CircuitSetup/Split-Single-Phase-Energy-Meter/Hardware/energy_meter_pcb_v1.3_back.PNG

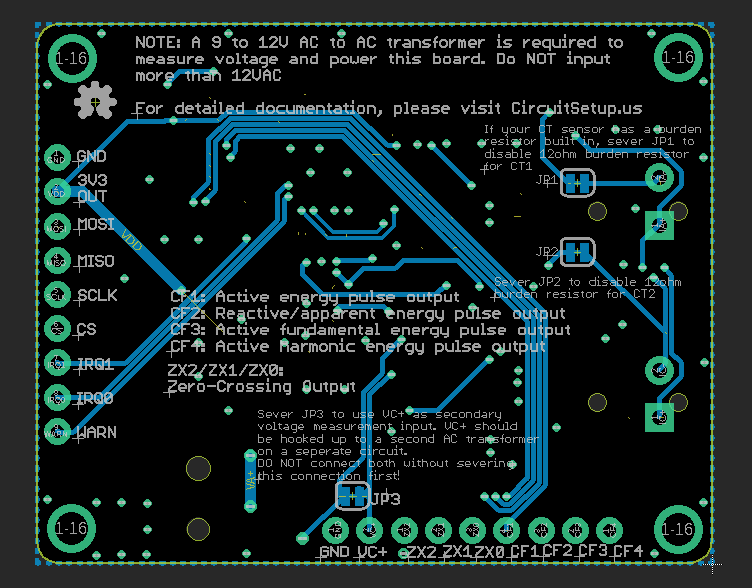
Hardware/energy_meter_pcb_v1.3_back.PNG
