CircuitSetup/Split-Single-Phase-Energy-Meter/Hardware/energy_meter_pcb_v1.4.png

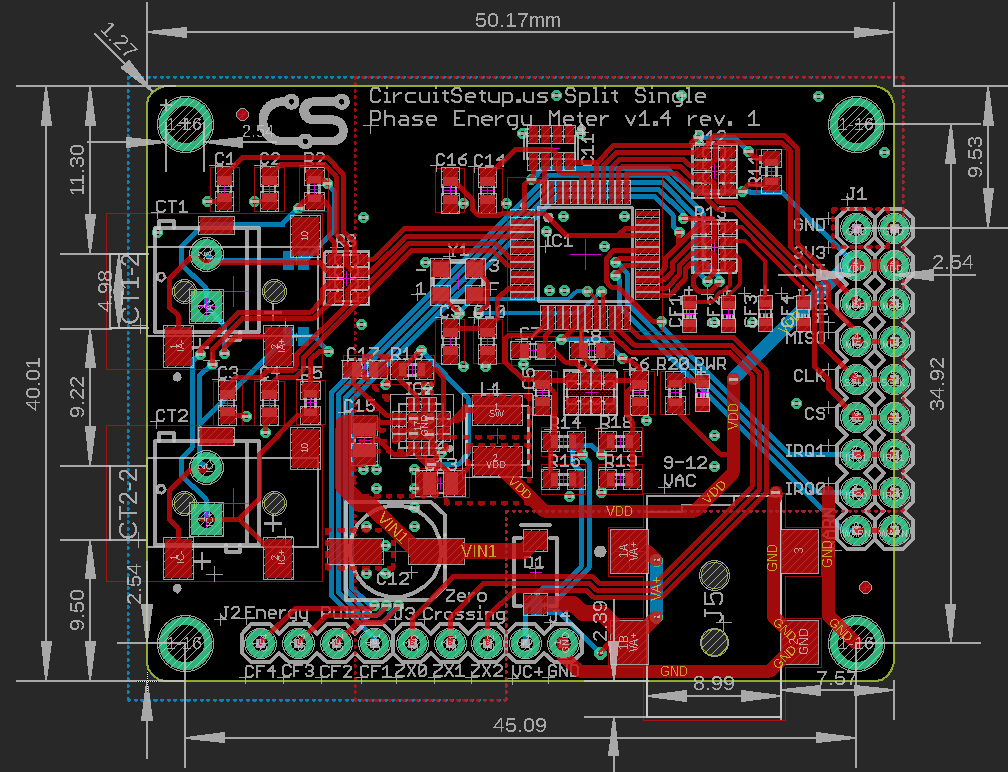
Hardware/energy_meter_pcb_v1.4.png
