CircuitSetup/Split-Single-Phase-Energy-Meter/Hardware/energy_meter_schematic.png

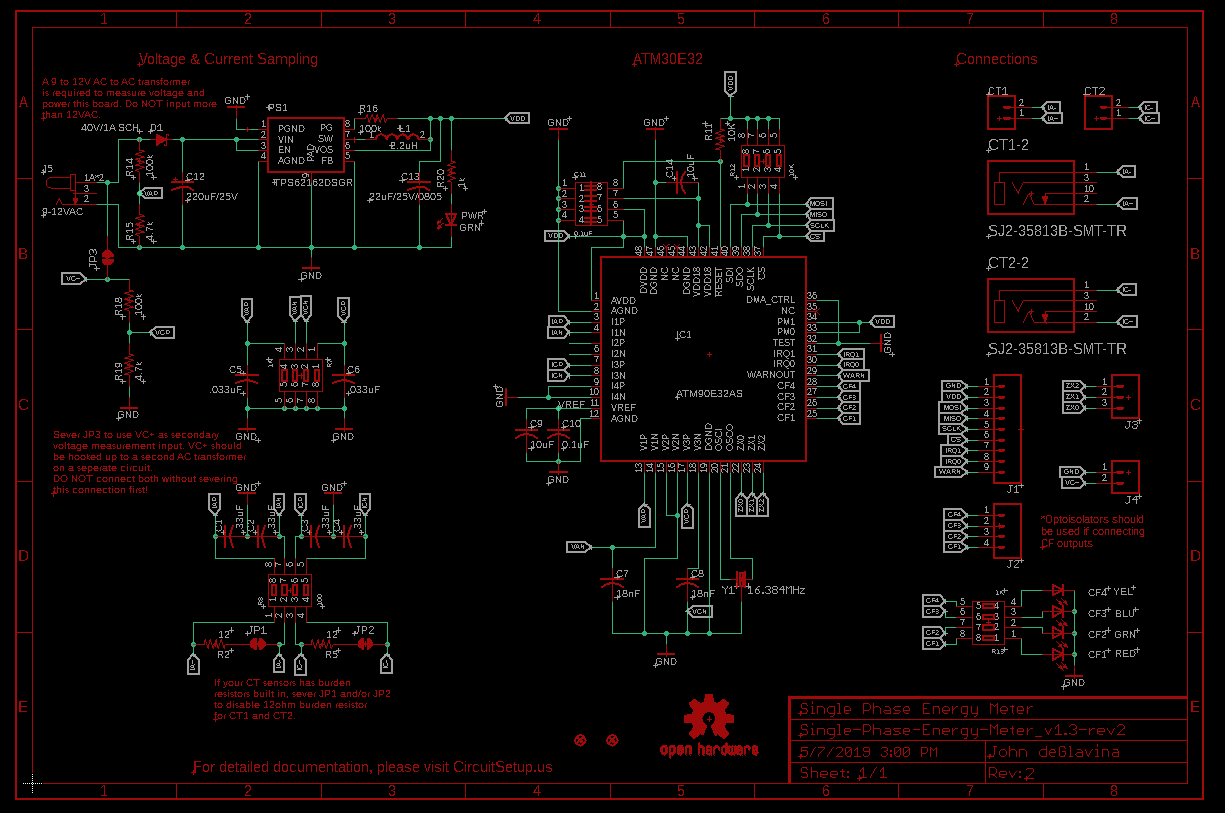
Hardware/energy_meter_schematic.png
