CircuitSetup/Split-Single-Phase-Energy-Meter/Hardware/energy_meter_schematic_v1.4.png

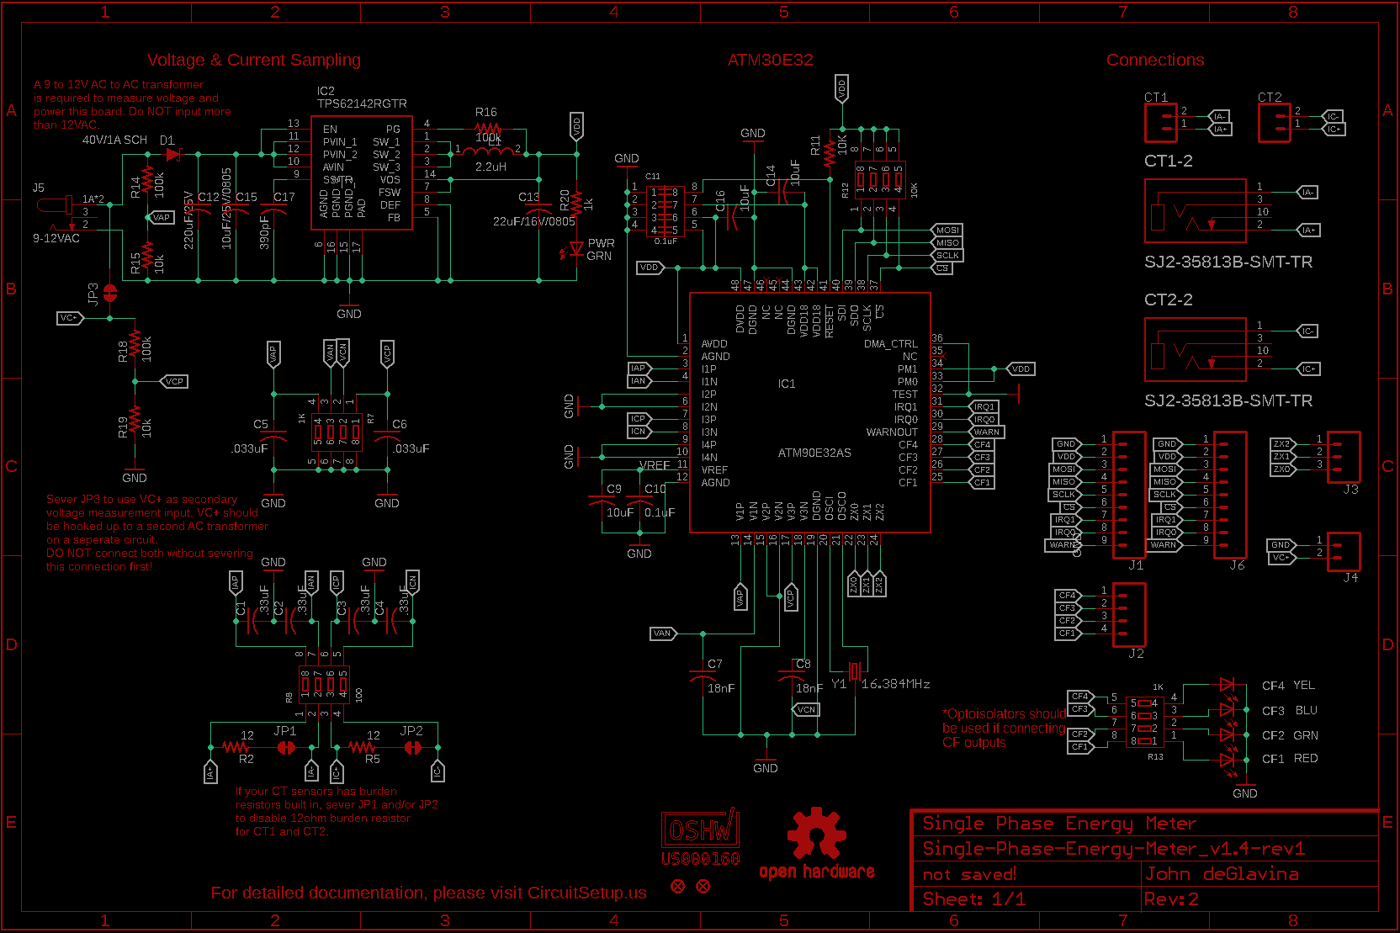
Hardware/energy_meter_schematic_v1.4.png
