CircuitSetup/Split-Single-Phase-Energy-Meter/Hardware/solar_adapter_esp32-oled.PNG

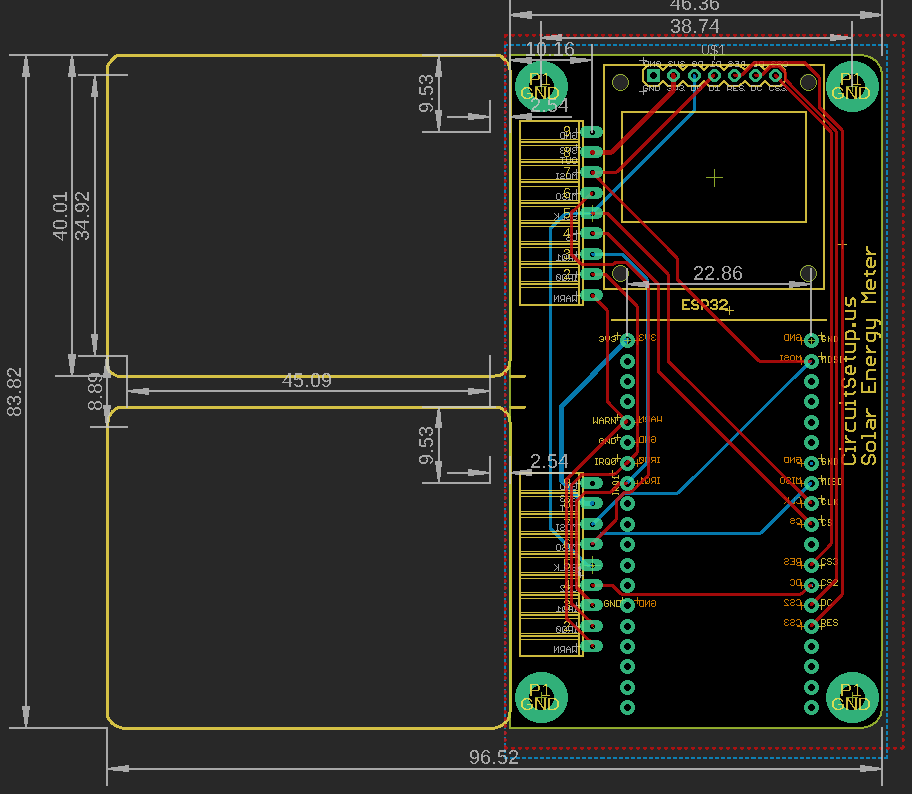
Hardware/solar_adapter_esp32-oled.PNG
