CircuitSetup/Split-Single-Phase-Energy-Meter/images/2EwjojQ.png

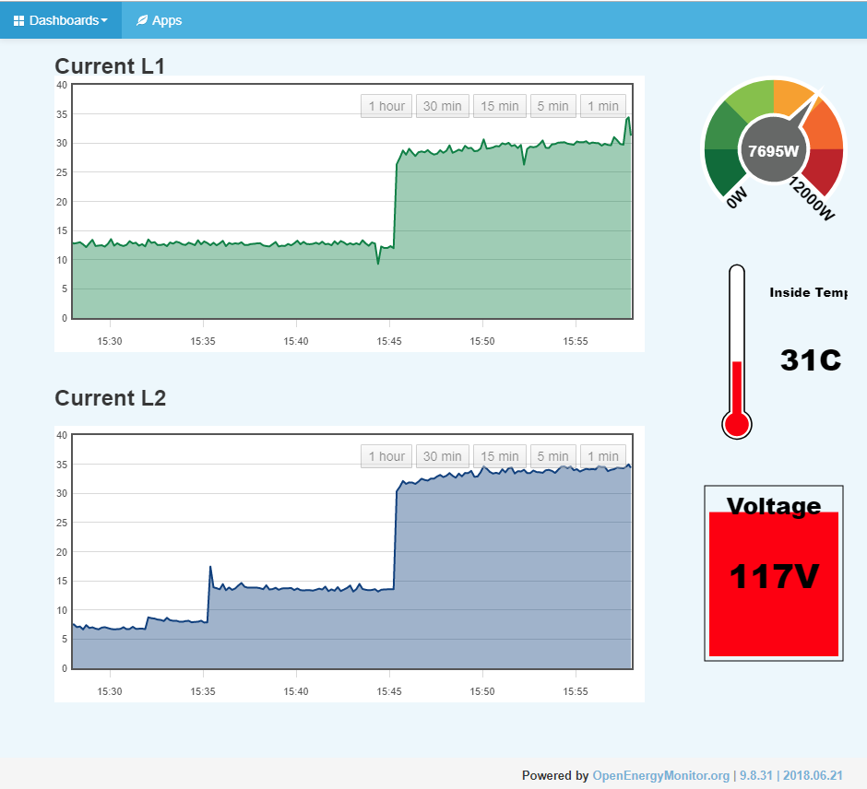
images/2EwjojQ.png
