CircuitSetup/Split-Single-Phase-Energy-Meter/images/9XtFifv.png

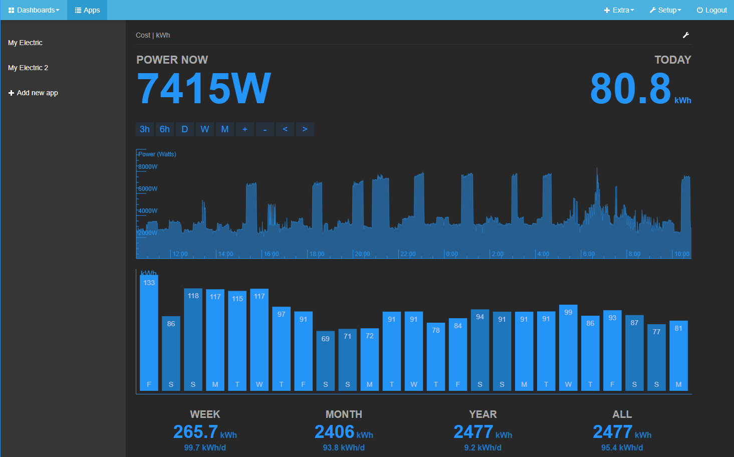
images/9XtFifv.png
