CircuitSetup/Split-Single-Phase-Energy-Meter/images/61TatPPej5L._SL1000_.jpg

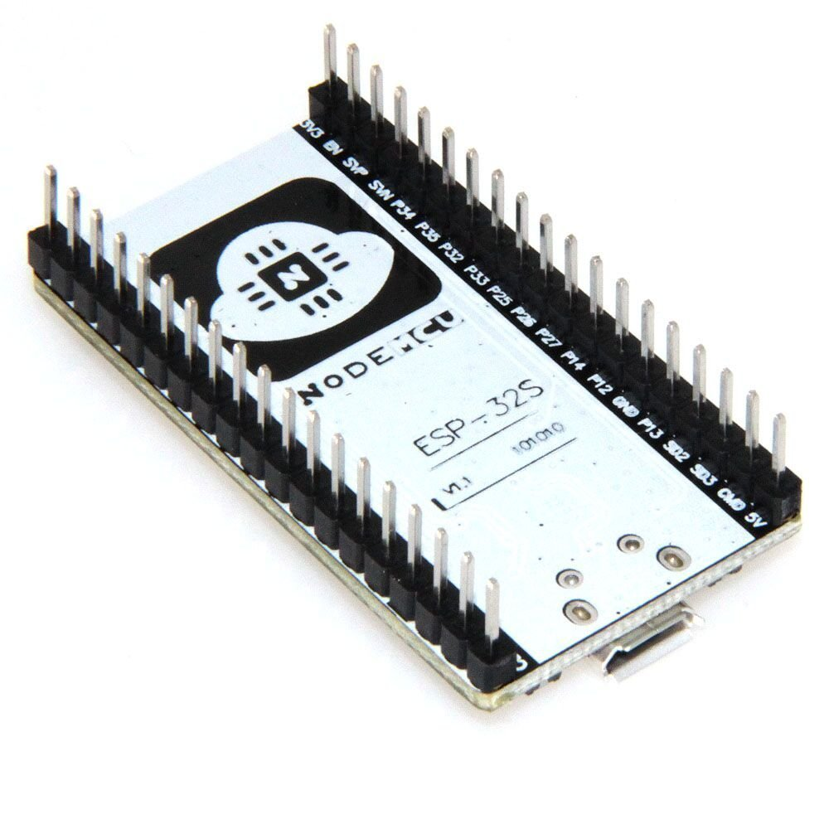
images/61TatPPej5L._SL1000_.jpg
