CircuitSetup/Split-Single-Phase-Energy-Meter/images/613Q6IxkivL._SL1000_.jpg

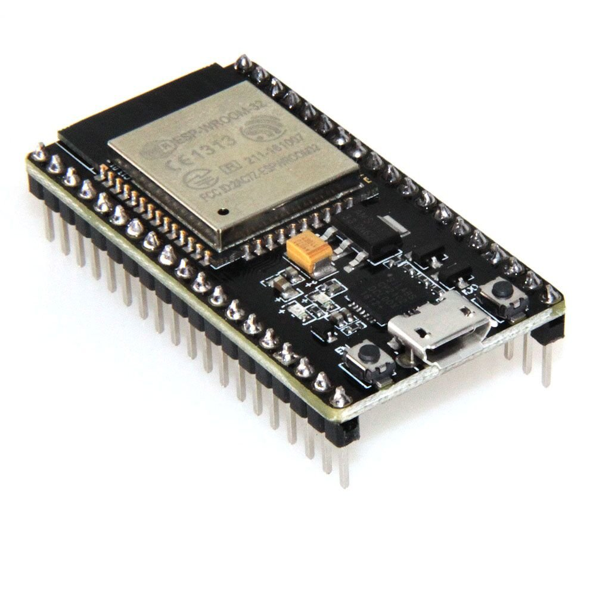
images/613Q6IxkivL._SL1000_.jpg
