CircuitSetup/Split-Single-Phase-Energy-Meter/images/157041.jpg

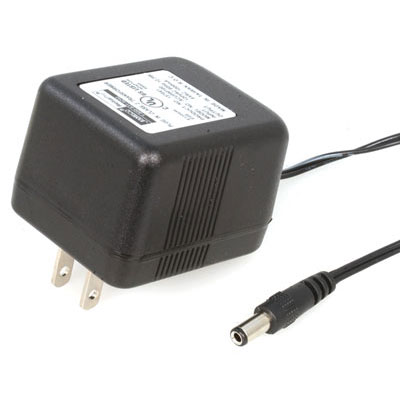
images/157041.jpg
