CircuitSetup/Split-Single-Phase-Energy-Meter/images/current_transformer_SCT016-2.jpg

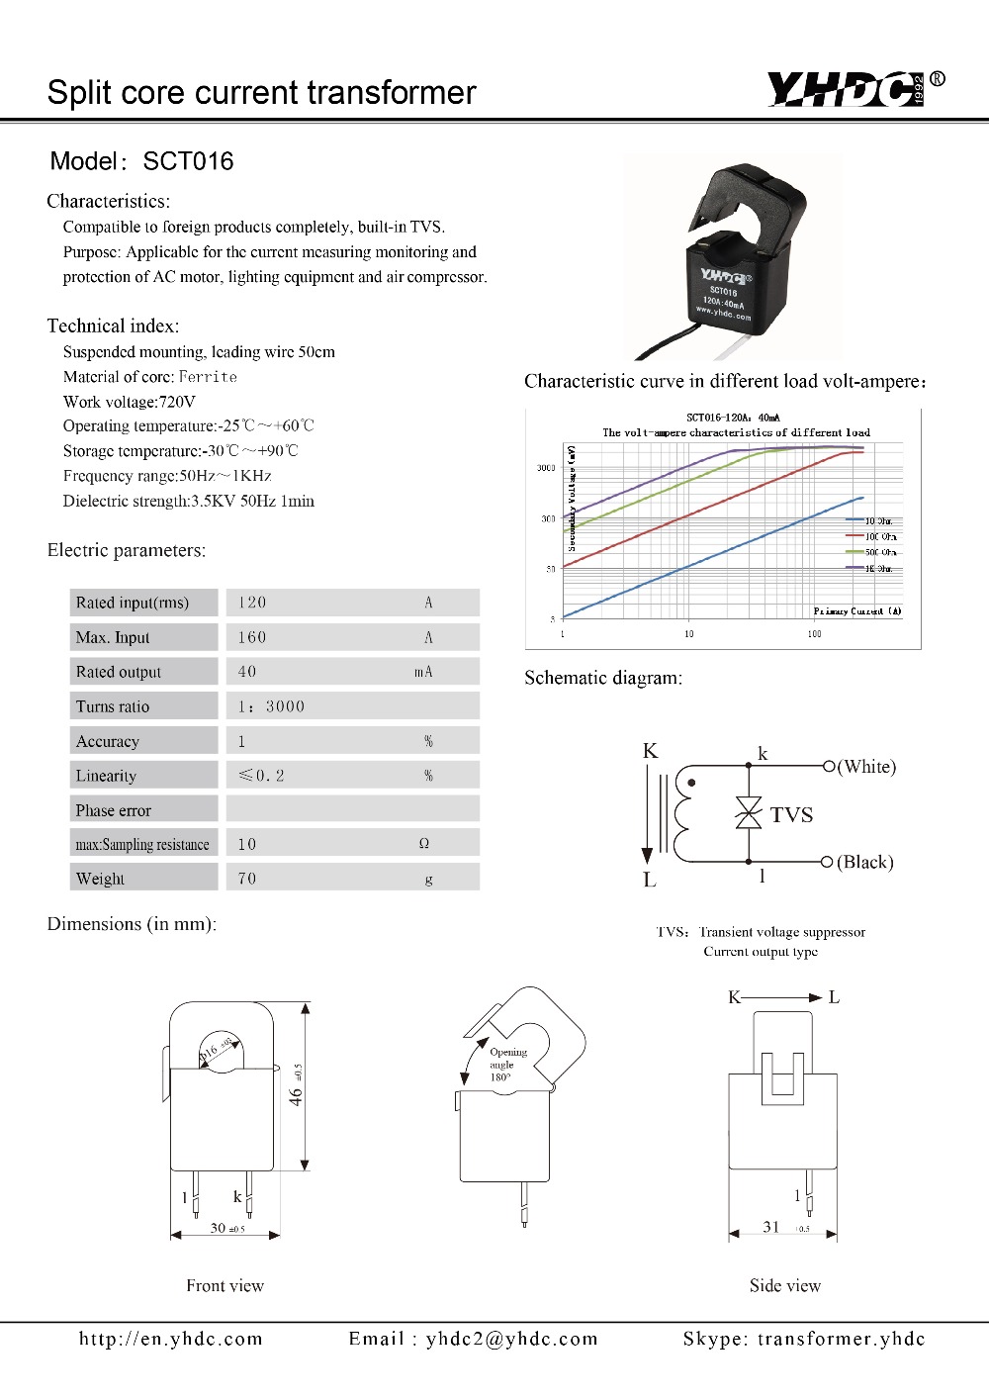
images/current_transformer_SCT016-2.jpg
