CircuitSetup/Split-Single-Phase-Energy-Meter/images/energy_meter_output.PNG

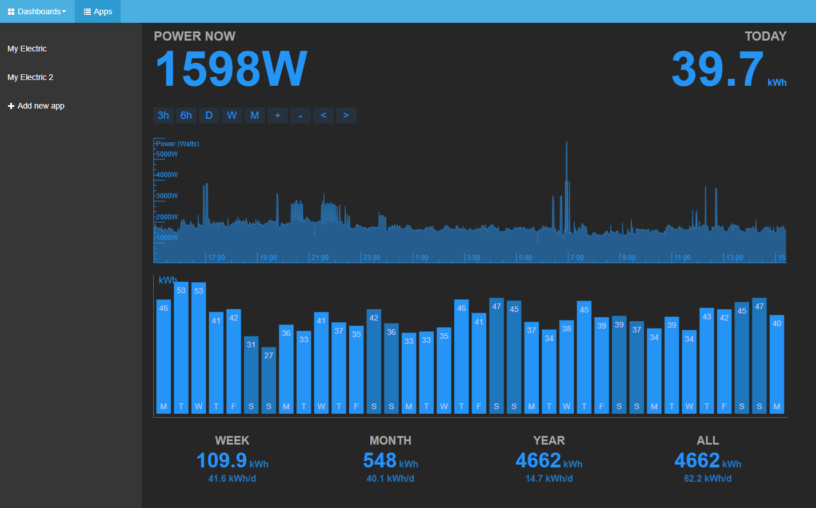
images/energy_meter_output.PNG
