CircuitSetup/Split-Single-Phase-Energy-Meter/images/energy_meter_pcb.jpg

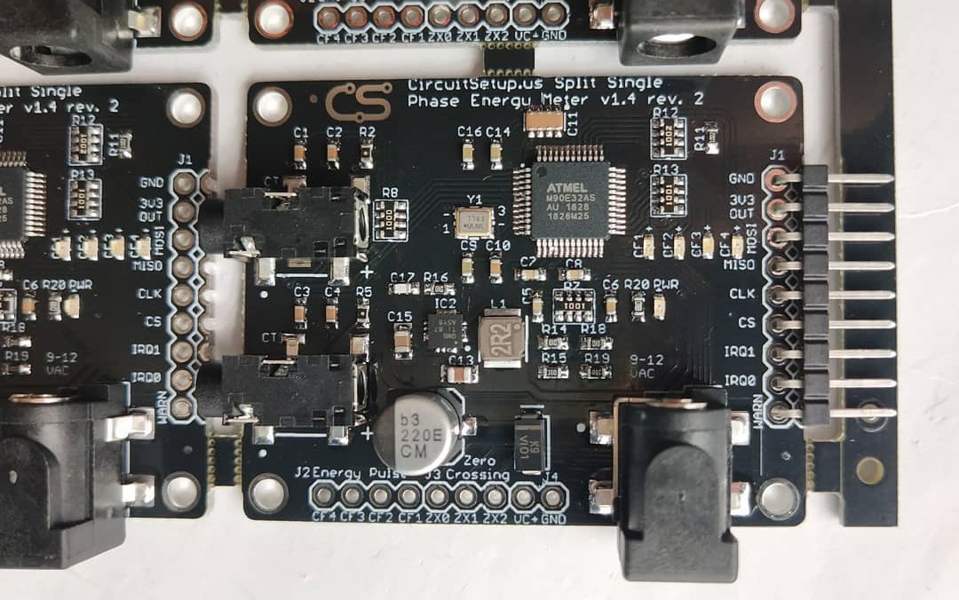
images/energy_meter_pcb.jpg
