CircuitSetup/Split-Single-Phase-Energy-Meter/images/energy_meter_rendering2.jpg

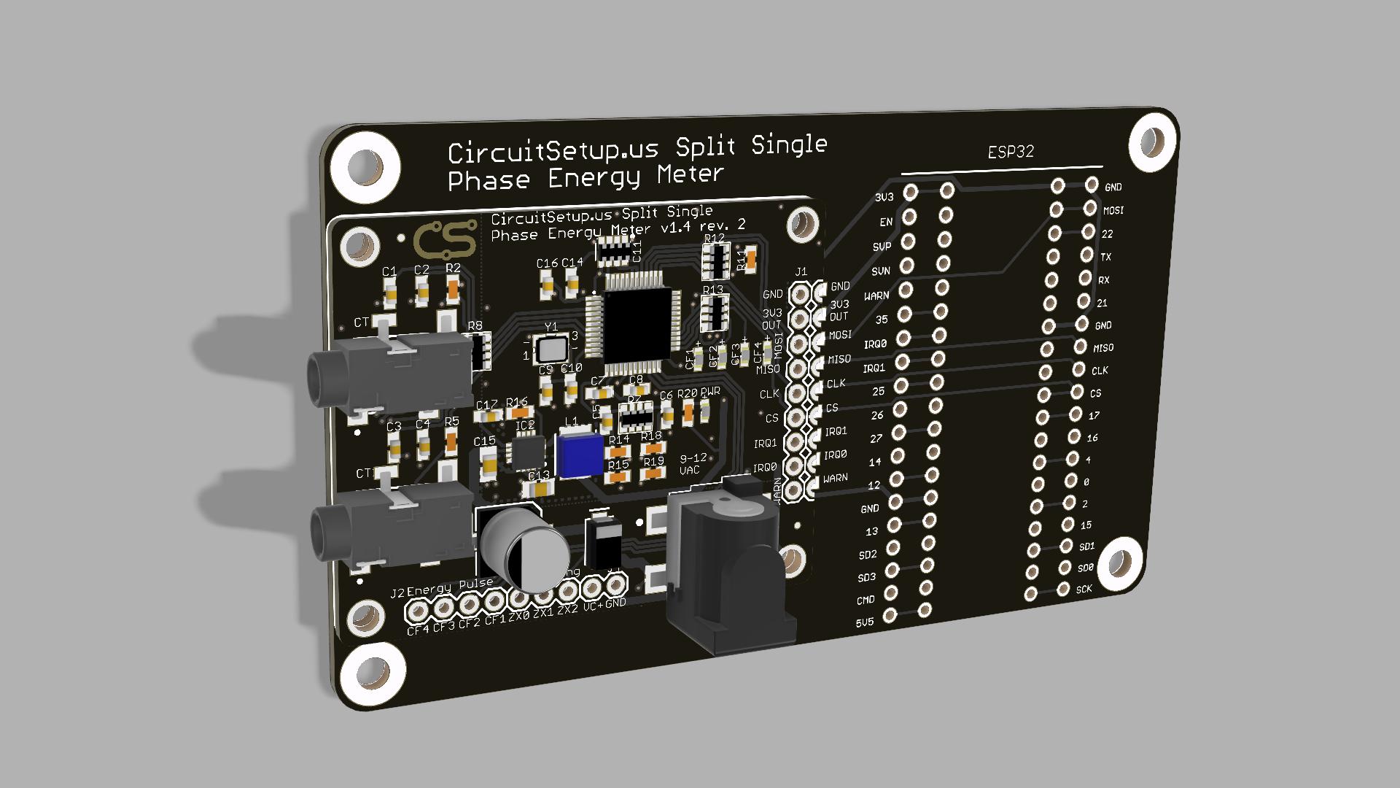
images/energy_meter_rendering2.jpg
