CircuitSetup/Split-Single-Phase-Energy-Meter/images/energy_meter_rendering3.jpg

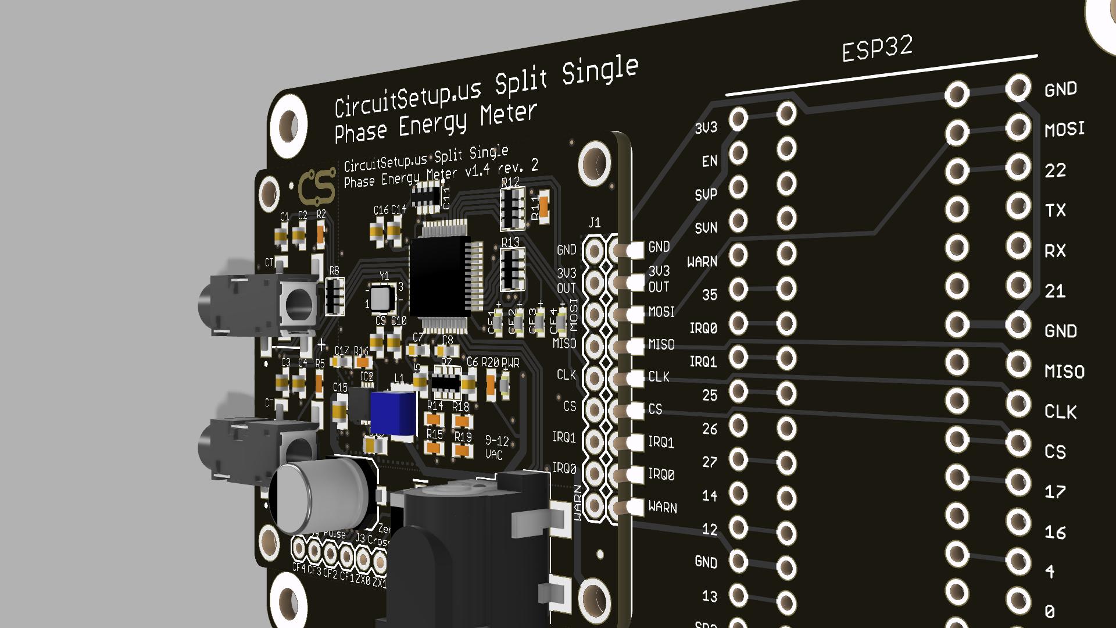
images/energy_meter_rendering3.jpg
