CircuitSetup/Split-Single-Phase-Energy-Meter/images/energy_meter_rendering.jpg

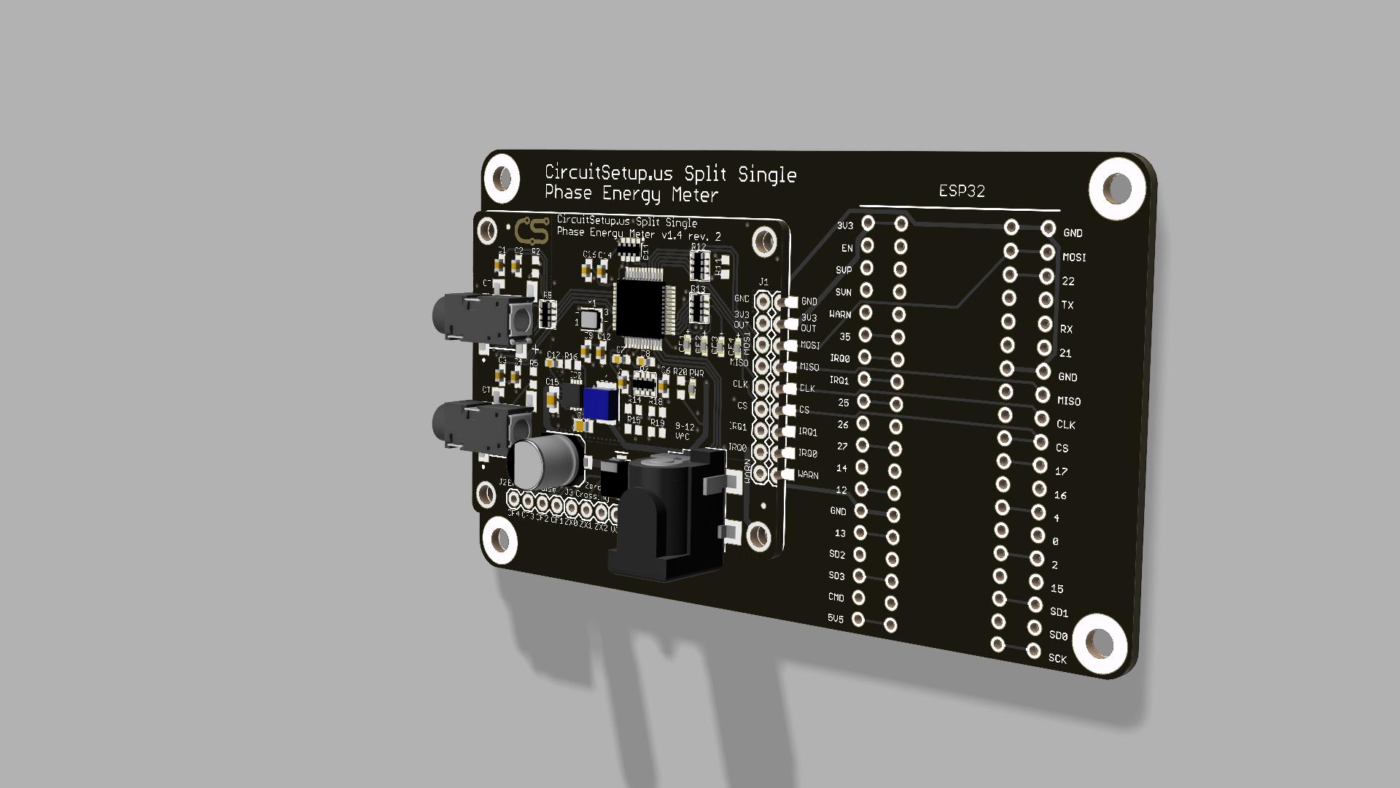
images/energy_meter_rendering.jpg
