CircuitSetup/Split-Single-Phase-Energy-Meter/images/energy_meter_solar_kit2.jpg

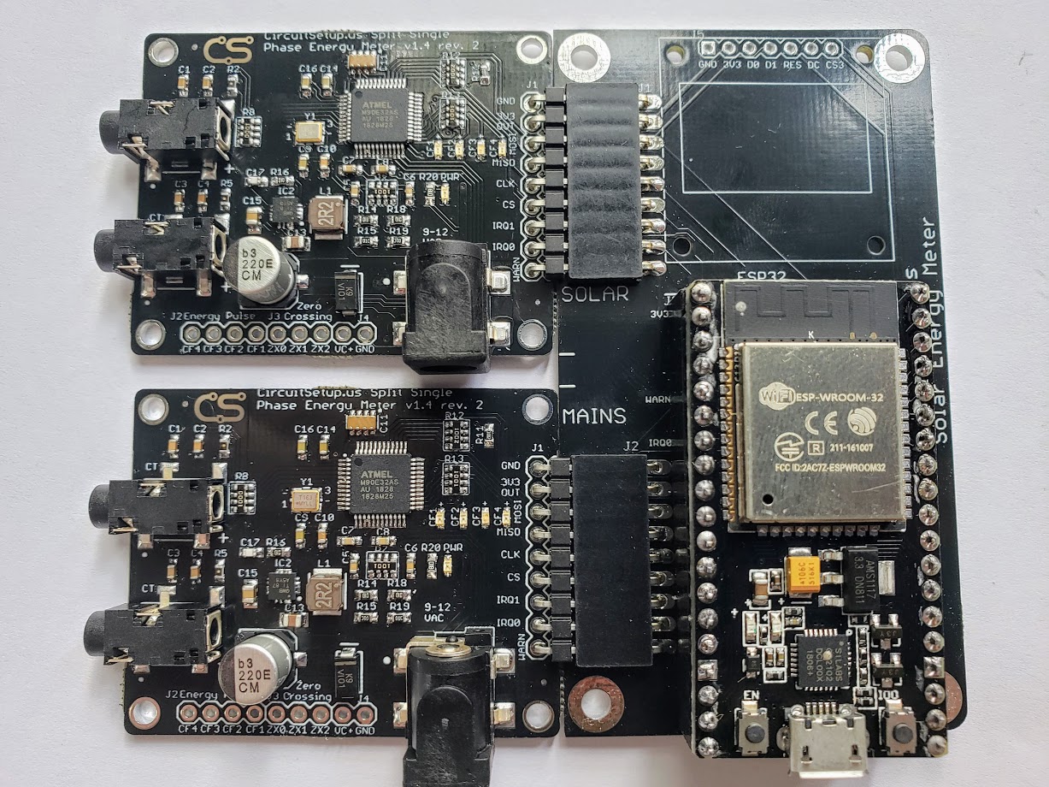
images/energy_meter_solar_kit2.jpg
