CircuitSetup/Split-Single-Phase-Energy-Meter/images/energy_meter_v1.4_back.jpg

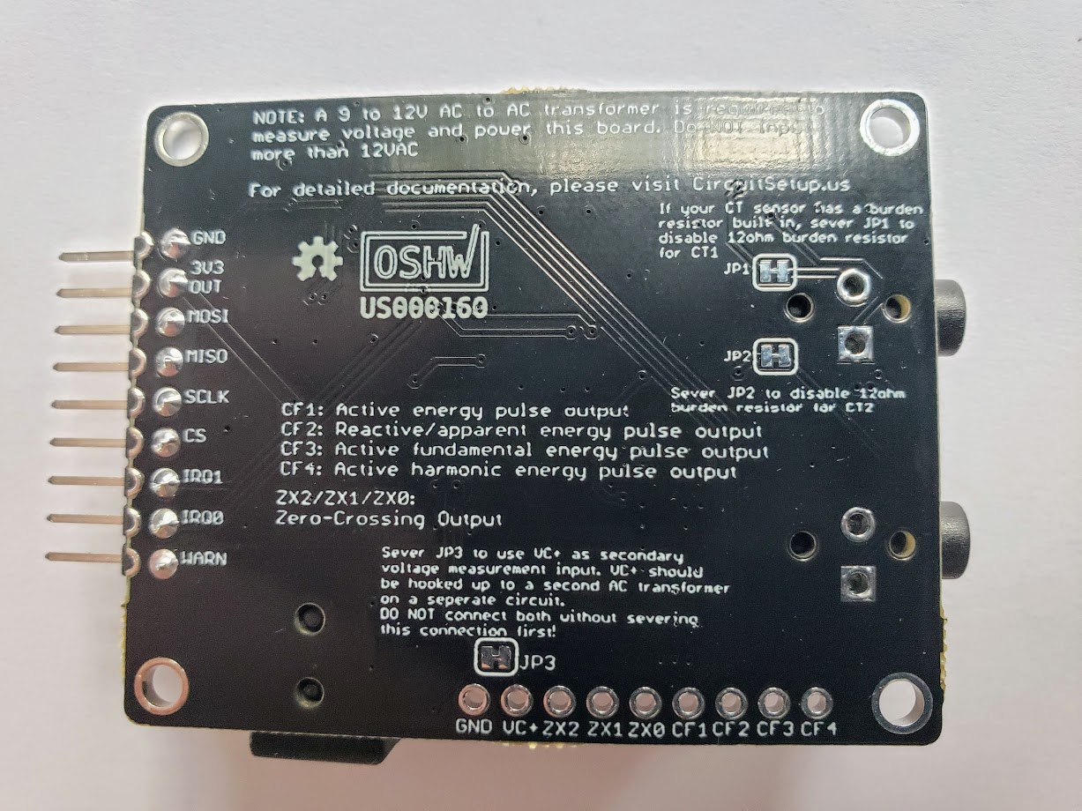
images/energy_meter_v1.4_back.jpg
