CircuitSetup/Split-Single-Phase-Energy-Meter/images/LSnrkSQ.png

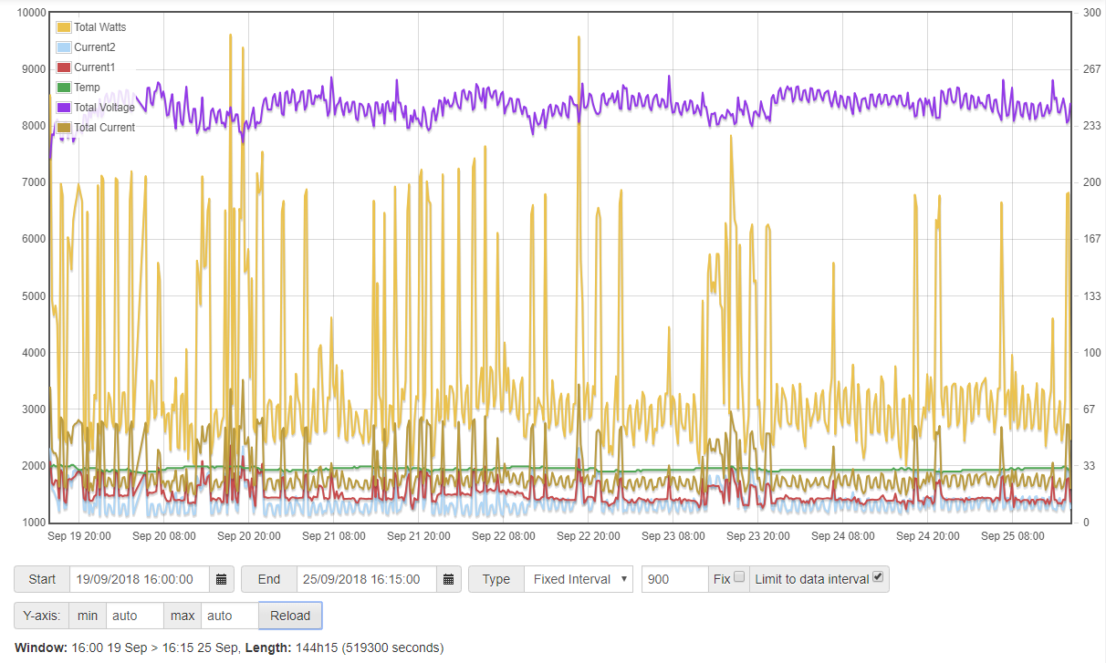
images/LSnrkSQ.png
