CircuitSetup/Split-Single-Phase-Energy-Meter/images/MpiP78N.png

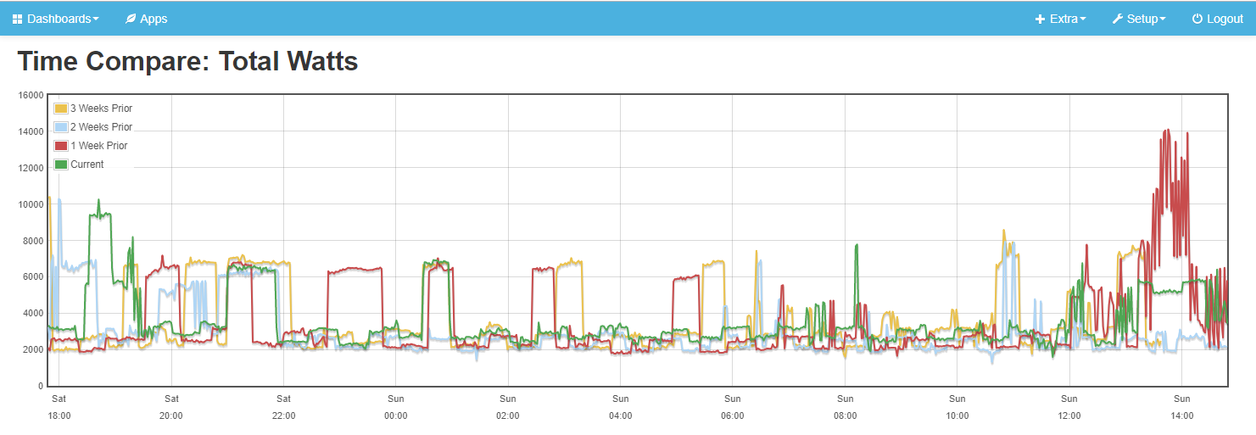
images/MpiP78N.png
