CircuitSetup/Split-Single-Phase-Energy-Meter/images/nodemcu_32s_sch.png

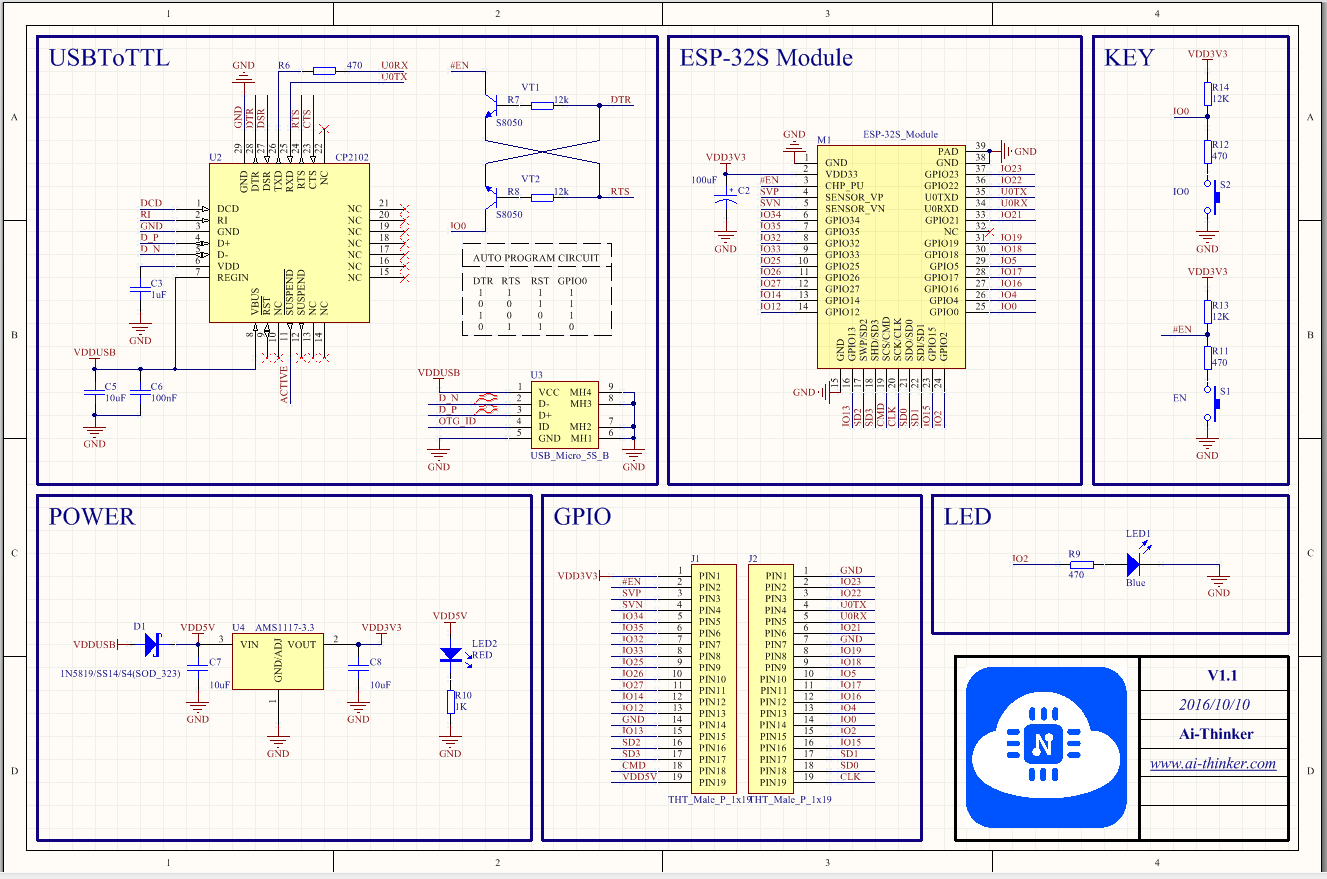
images/nodemcu_32s_sch.png
