CircuitSetup/Split-Single-Phase-Energy-Meter/images/nodemcu_32s_size2.png

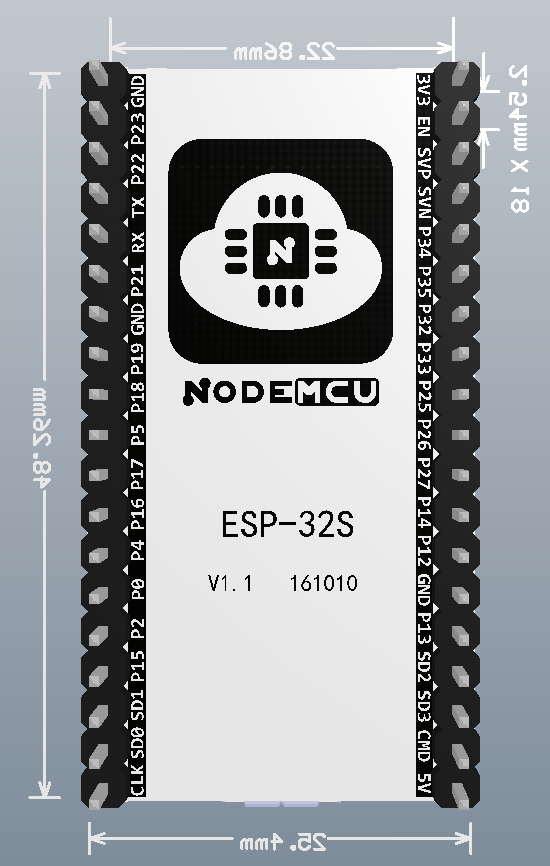
images/nodemcu_32s_size2.png
