CircuitSetup/Split-Single-Phase-Energy-Meter/images/spiltsinglephase-cables-front_png_project-body.jpg

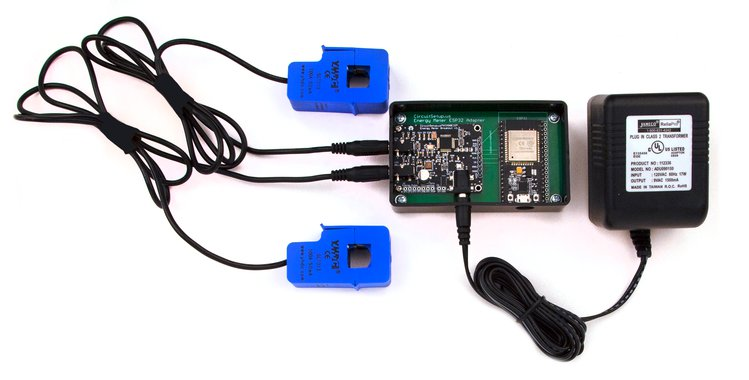
images/spiltsinglephase-cables-front_png_project-body.jpg
