CircuitSetup/Split-Single-Phase-Energy-Meter/images/voltage_grafana.PNG

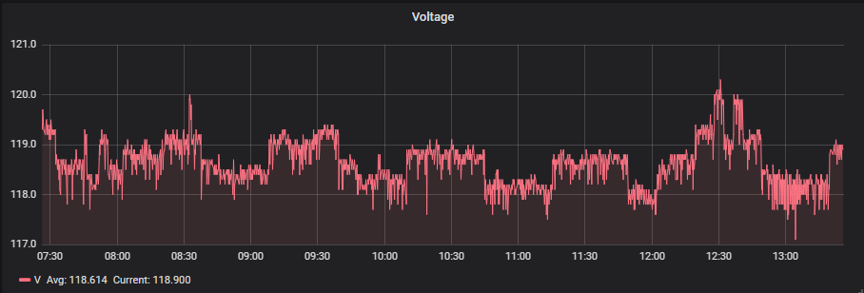
images/voltage_grafana.PNG
