CircuitSetup/Split-Single-Phase-Energy-Meter/images/CircuitSetup_Final File.png

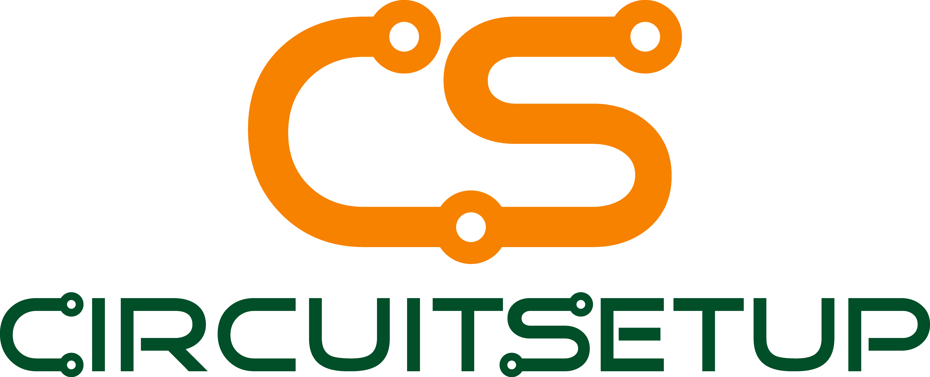
images/CircuitSetup_Final File.png
