CircuitSetup/Split-Single-Phase-Energy-Meter/images/current_transformer_SCT016-install.jpg

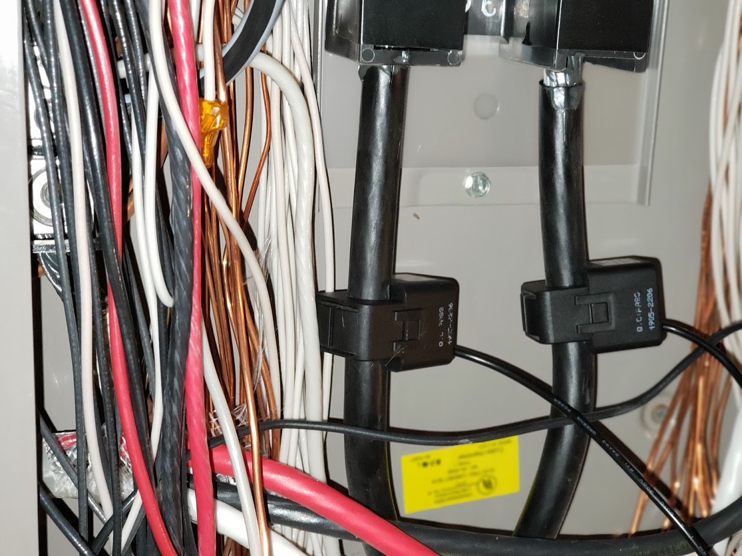
images/current_transformer_SCT016-install.jpg
